Jchisholm204/Scout/src/control_board/firmware/core/include/main.h

/**
 * @file main.h
 * @author Jacob Chisholm (Jchisholm204.github.io)
 * @brief 
 * @version 0.1
 * @date 2023-11-06
 * 
 * @copyright Copyright (c) 2023
 * 
 */

#ifndef _MAIN_HPP_
#define _MAIN_HPP_

#include <stm32f4xx.h>
#include "config/nvic.h"
#include "FreeRTOS.h"
#include "task.h"

extern void SystemInit(void);

extern int main(void);

#endif
