Jchisholm204/Scout/src/control_board/firmware/core/src/tasks/gravity_planner_tsk.c

/**
 * @file gravity_planner_tsk.c
 * @author Jacob Chisholm (https://Jchisholm204.github.io)
 * @brief
 * @version 0.1
 * @date Created: 2025-10-17
 * @modified Last Modified: 2025-10-17
 *
 * @copyright Copyright (c) 2025
 */

#include "tasks/gravity_planner_tsk.h"
#include "FreeRTOS.h"

void vGPlanTsk(void *pvParams);

QueueHandle_t gplan_tsk_init(struct gplan_tsk *pHndl,
                             QueueHandle_t usb_rx,
                             QueueHandle_t usb_tx) {
    if (!pHndl) {
        return NULL;
    }
    // Initialize the usb queues
    pHndl->usb.rx = usb_rx;
    pHndl->usb.tx = usb_tx;

    // Setup the Collision Vector Output Queue
    pHndl->cv_tx.hndl = xQueueCreateStatic(GPLAN_CVTX_BUF_SIZE,
                                           sizeof(quat_t),
                                           (uint8_t *) pHndl->cv_tx.buf,
                                           &pHndl->cv_tx.static_queue);

    if (!pHndl->cv_tx.hndl) {
        return NULL;
    }

    // Setup the Gravity Planner Task
    pHndl->tsk.hndl = xTaskCreateStatic(vGPlanTsk,
                                        "gplan",
                                        GPLAN_TSK_STACK_SIZE,
                                        pHndl,
                                        configMAX_PRIORITIES-4,
                                        pHndl->tsk.stack,
                                        &pHndl->tsk.static_tsk);

    if (!pHndl->tsk.hndl) {
        return NULL;
    }

    return pHndl->cv_tx.hndl;
}

void vGPlanTsk(void *pvParams) {
    struct gplan_tsk *pHndl = (struct gplan_tsk *) pvParams;

    printf("Gplan Online\n");

    TickType_t last_wake_time = xTaskGetTickCount();

    for (;;) {
        static struct udev_pkt_lidar ldrpkt = {0};
        if (xQueueReceive(pHndl->usb.rx, &ldrpkt, 100) == pdTRUE) {
            xQueueSendToBack(pHndl->usb.tx, &ldrpkt, 10);
        }
        // vTaskDelayUntil(&last_wake_time, 1);
    }
}
