Jchisholm204/Scout/src/control_board/firmware/core/include/protocols/crsf/crsf_types_internal.h

/**
 * @file csrf_types_internal.h
 * @author Jacob Chisholm (https://Jchisholm204.github.io)
 * @brief Internal (packed) Types for internal usage in the CRSF Module
 * @version 0.1
 * @date Created: 2025-10-14
 * @modified Last Modified: 2025-10-14
 *
 * @copyright Copyright (c) 2025
 */

#ifndef _CRSF_TYPES_INT_H_
#define _CRSF_TYPES_INT_H_

#include <stdint.h>

#define CRSF_DATA_MAXLEN 64
#define CRSF_STR_LEN 10
#define CRSF_ADDR 0xC8

typedef struct __attribute__((packed)) {
    // degrees / 10_000_000
    int32_t lattitude;
    // degrees / 10_000_000
    int32_t longitude;
    // km/h / 100
    uint16_t groundspeed;
    // degree / 100
    uint16_t heading;
    // meter - 1000m offset
    uint16_t altitude;
    uint8_t sat_count;
} _crsf_gps_t;

typedef struct __attribute__((packed)) {
    // mV * 100
    uint16_t voltage;
    // mA * 100
    uint16_t current;
    // mAh (24 bits)
    uint8_t capacity[3];
    // percent (0-100]
    uint8_t percent_remaining;
} _crsf_battery_t;

typedef struct __attribute__((packed)) {
    // dBm *-1
    uint8_t uplink_RSSI_1;
    // dBm *-1
    uint8_t uplink_RSSI_2;
    // percent
    uint8_t uplink_quality;
    // uplink SNR (db)
    int8_t uplink_SNR;
    // enum ant 1 = 0, 2
    uint8_t diversity_active_antenna;
    // enum Mode (4fps = 0, 50fps, 150Hz)
    uint8_t RF_mode;
    // enum (0mW, 10mW, 25mW, 100mW, 500mW, 1000mW, 2000mW)
    uint8_t tx_power;
    // dBm * -1
    uint8_t downlink_RSSI;
    // percent
    uint8_t downlink_quality;
    // db
    int8_t downlink_SNR;
} _crsf_link_t;

typedef struct __attribute__((packed)) {
    unsigned int chan0 : 11;
    unsigned int chan1 : 11;
    unsigned int chan2 : 11;
    unsigned int chan3 : 11;
    unsigned int chan4 : 11;
    unsigned int chan5 : 11;
    unsigned int chan6 : 11;
    unsigned int chan7 : 11;
    unsigned int chan8 : 11;
    unsigned int chan9 : 11;
    unsigned int chan10 : 11;
    unsigned int chan11 : 11;
    unsigned int chan12 : 11;
    unsigned int chan13 : 11;
    unsigned int chan14 : 11;
    unsigned int chan15 : 11;
} _crsf_rc_t;

typedef struct __attribute__((packed)) {
    int16_t pitch;
    int16_t roll;
    int16_t yaw;
} _crsf_attitude_t;

typedef struct __attribute__((packed)) {
    char mode[CRSF_STR_LEN];
} _crsf_fcmode_t;

typedef struct __attribute__((packed)) {
    uint8_t addr;
    uint8_t length;
    uint8_t type;
    union {
        uint8_t pyld[CRSF_DATA_MAXLEN];
        _crsf_link_t link;
        _crsf_battery_t batt;
        _crsf_rc_t rc;
        _crsf_attitude_t att;
        _crsf_fcmode_t mode;
    };
} _crsf_msg_t;

#endif
