Jchisholm204/Scout/src/simulation/control/src/main.cpp

#include <rclcpp/rclcpp.hpp>
#include <std_msgs/msg/float32.hpp>
#include "control/control_node.hpp"

int main(int argc, char **argv) {
    rclcpp::init(argc, argv);
    rclcpp::spin(std::make_shared<ControlNode>());
    rclcpp::shutdown();
    std::cout << "Hello World!" << std::endl;
    return 0;
}
